ingobeans/ittypda/firmware/devboard/Core/Inc/conf.h

#define LCD_CS GPIO_PIN_0
#define LCD_CS_PORT GPIOA
#define LCD_RST GPIO_PIN_1
#define LCD_RST_PORT GPIOA
#define LCD_RS GPIO_PIN_2
#define LCD_RS_PORT GPIOA

#define LED GPIO_PIN_3
#define LED_PORT GPIOA

#define DEBUG_LED GPIO_PIN_13
#define DEBUG_LED_PORT GPIOC
#define DEBUG_LED_ON_STATE 0

// technically out of spec i think but my sd card allows it :>
#define SD_MOUNT_SPI_SPEED SPI_BAUDRATEPRESCALER_4
#define SD_SPI_SPEED SPI_BAUDRATEPRESCALER_4
#define LCD_SPI_SPEED SPI_BAUDRATEPRESCALER_2

// #define MOSI GPIO_PIN_7
// #define MOSI_PORT GPIOA
// #define MISO GPIO_PIN_6
// #define MISO_PORT GPIOA
// #define SCK GPIO_PIN_5
// #define SCK_PORT GPIOA

#define SD_CS GPIO_PIN_4
#define SD_CS_PORT GPIOA

#define HSPI hspi1
